KenwoodFox/EG-207/docs/advanced_service/flowcharts/flowchart.png

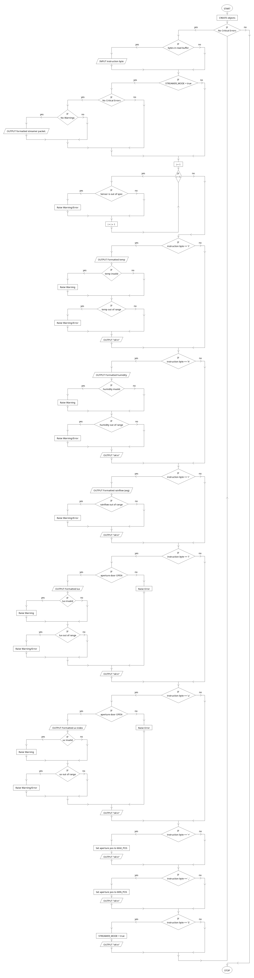
docs/advanced_service/flowcharts/flowchart.png
