KenwoodFox/EG-207/docs/presentations/resources/SNHU-CETA.png

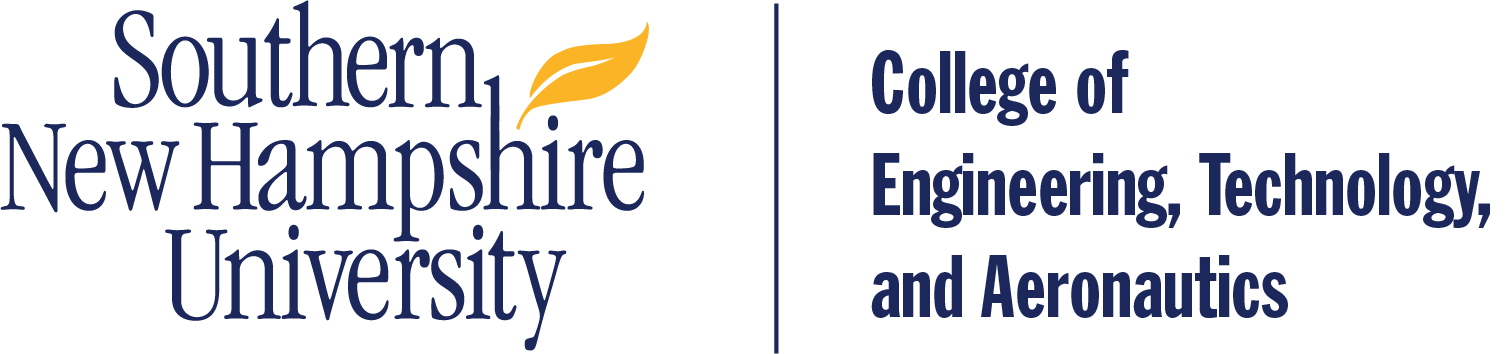
docs/presentations/resources/SNHU-CETA.png
