KenwoodFox/EG-207/docs/presentations/resources/SNHU.png

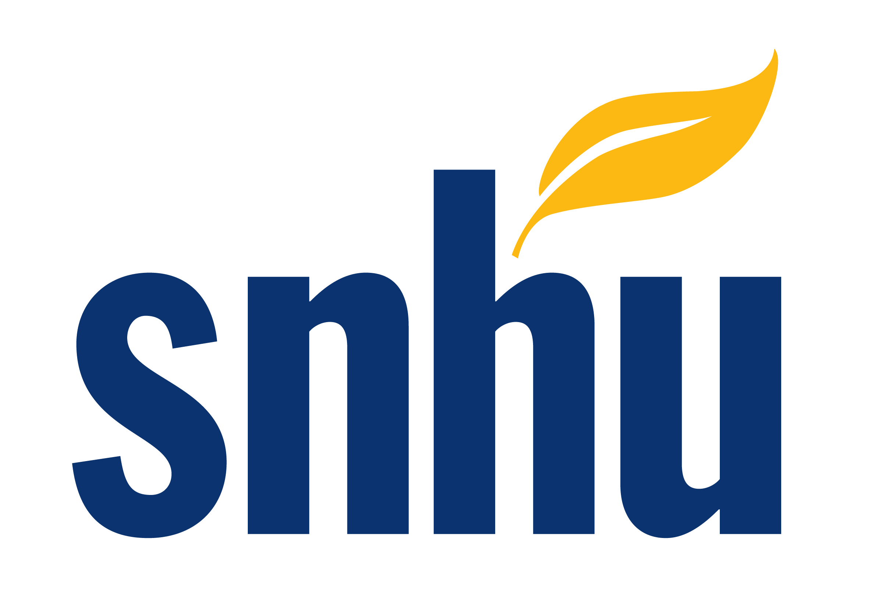
docs/presentations/resources/SNHU.png
