KenwoodFox/EG-207/CAD/schematics/lab2/lab2.sch

## KiCad design CAD/schematics/lab2/lab2.sch (2021-11-01)

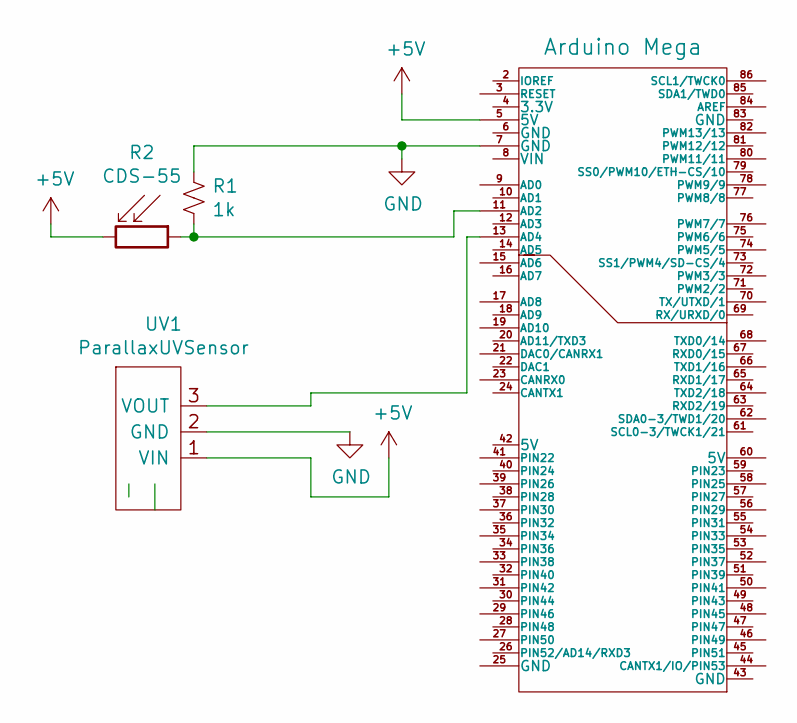
[picture p62: schematic lab2.sch]

Parts:
R1: 1k
R2: CDS-55
UV1: ParallaxUVSensor

Connections:
+5V: R2.2, UV1.1 (VIN)
GND: R1.1, UV1.2 (GND)
unnamed: R1.2, R2.1
