KenwoodFox/EG-207/python/goldstandard/goldplot.py

# Team Gold
# EG-207
# Southern New Hampshire University, 2021

import re
import csv
import time
import serial
import logging
import argparse
import subprocess

import matplotlib.pyplot as plt
import matplotlib.animation as animation
import matplotlib as mpl

from statistics import mean


class GoldPlotApp:
    def __init__(self, logger, **kwargs):
        # logging
        self.log = logger

        # Graph theme
        mpl.style.use('seaborn')

        # Parse args
        parser = argparse.ArgumentParser(description='Parse args.')
        parser.add_argument('--port',
                            nargs='?',
                            default='/dev/ttyACM0',
                            type=str)

        parser.add_argument('--data',
                            nargs='?',
                            default=None,
                            type=str)

        parser.add_argument('-o',
                            nargs='?',
                            default='output.csv',
                            type=str)

        parser.add_argument('--hist',
                            action='store_true')

        self.args = parser.parse_args()

        # Arduino version
        self.arduino_version = None

        # Software version
        self.software_version = self.get_git_revision_hash()

        # Setup graph
        self.initalize_graph()

        if self.args.data is None:
            # Log
            self.log.info("Initalizing arduino.")

            # Connect arduino
            self.arduino = serial.Serial(self.args.port, 115200, timeout=1)

            # Data for this run
            self.csv_data = open(self.args.o, 'w')
            self.csv_writer = csv.writer(self.csv_data, delimiter=',',
                                         quotechar='"',
                                         quoting=csv.QUOTE_MINIMAL)
            self.csv_writer.writerow(['Epoch Time', 'Temp', 'Humidity', 'Lux Level', 'UV Index'])  # noqa: E501

        else:
            # Load csv data instead.
            self.log.debug("Loading CSV.")
            with open(self.args.data, mode='r') as datafile:
                csv_reader = csv.DictReader(datafile)
                for row in csv_reader:
                    if isinstance(row['Epoch Time'], str):
                        _time = row["Epoch Time"]
                        _temp = row["Temp"]
                        _humid = row["Humidity"]

                        self.time_scale.append(float(_time))
                        self.temp_reading.append(float(_temp))
                        self.humidity_reading.append(float(_humid))

    def run(self):
        if self.args.data is None:
            # Setup animated graph.
            ani = animation.FuncAnimation(self.fig,
                                          self.update_graph,
                                          interval=2)

            # Just for flake
            ani.__str__()
        else:
            self.log.debug("Got to run")

            self.update_graph(0)

        # Show plot!
        plt.show()

    def get_new_frame(self):
        # Time
        now = float(time.time())
        # Frame is one data frame
        frame = self.arduino.readline().decode().strip('\n\r')

        try:
            ver_match = re.search('(?<=version )(.*)', frame).group(0)
            if ver_match is not None:
                self.arduino_version = str(ver_match)
        except AttributeError:
            pass

        try:
            if len(frame) > 0:
                # Capture a new frame
                frame = frame.split(',')
                self.log.debug(f'Raw frame is {frame}')

                self.current_humidy = float(frame[0].strip('H'))
                self.current_temp = float(frame[1].strip('T'))
                self.current_lux_level = float(frame[2].strip('L'))
                self.current_uv_index = float(frame[3].strip('U'))

                if self.current_humidy != 0 and self.current_temp != 0:
                    # Logging
                    self.log.info(f'Got new frame: {frame}')

                    # Plot scales
                    self.time_scale.append(now)
                    self.temp_reading.append(self.current_temp)
                    self.humidity_reading.append(self.current_humidy)
                    self.lux_reading.append(self.current_lux_level)
                    self.index_reading.append(self.current_uv_index)
                else:
                    logging.error(f'Error, empty frame: {frame}')
        except (IndexError, AttributeError, ValueError) as e:
            self.log.warn('Got bad frame')
            self.log.error(e)

        # Trigger a csv update
        self.write_csv()

    def write_csv(self):
        try:
            self.csv_writer.writerow([self.time_scale[-1],
                                     self.temp_reading[-1],
                                     self.humidity_reading[-1],
                                     self.lux_reading[-1],
                                     self.index_reading[-1]])
            self.log.info(f'Wrote {self.current_lux_level} to data.')
        except IndexError:
            self.log.warn("Not writing bad frame to csv.")

    def initalize_graph(self):
        # Setup figure
        self.fig = plt.figure()
        self.ax = self.fig.add_subplot(111)
        self.temp_line_plot = self.fig.add_subplot(2, 1, 1)
        self.humidity_line_plot = self.fig.add_subplot(2, 1, 2)

        # Mess
        self.time_scale = []
        self.temp_reading = []
        self.max_temp = 0
        self.max_temp_time = 0
        self.humidity_reading = []
        self.index_reading = []
        self.lux_reading = []
        self.current_humidy = float(0)
        self.current_temp = float(0)

        # Spacing
        self.fig.tight_layout(pad=3.0)

        # Turn off axis lines and ticks of the big subplot
        self.ax.spines['top'].set_color('none')
        self.ax.spines['bottom'].set_color('none')
        self.ax.spines['left'].set_color('none')
        self.ax.spines['right'].set_color('none')
        self.ax.tick_params(labelcolor='w',
                            top=False,
                            bottom=False,
                            left=False,
                            right=False)

        self.ax.set_xlabel('Time (Epoch)')

        self.temp_line_plot.set_title('Temp')
        self.humidity_line_plot.set_title('Humidity')

        self.ax.annotate(f"""Software Version {self.software_version}
                             Arduino Version {self.arduino_version}""",
                         xy=(0.3, -0.13),
                         xycoords='axes fraction',
                         horizontalalignment='right',
                         verticalalignment='top')

        self.ax.annotate('Gold Standard, Team Gold, SNHU',
                         xy=(0.2, 1.1),
                         xycoords='axes fraction',
                         horizontalalignment='right',
                         verticalalignment='top')

    def update_graph(self, i):
        try:
            if self.args.data is None:
                # Get new frame
                self.get_new_frame()

            self.temp_line_plot.clear()
            self.temp_line_plot.plot(self.time_scale,
                                     self.lux_reading,
                                     color="red")

            self.humidity_line_plot.clear()
            self.humidity_line_plot.plot(self.time_scale,
                                         self.humidity_reading,
                                         color="blue")

            # === Annotations ===
            # Max temp
            self.max_temp = max(self.temp_reading)
            self.max_temp_time = self.time_scale[
                                 self.temp_reading.index(self.max_temp)]
            self.log.debug(f"Max temp {self.max_temp}")

            # Standard deviation math
            self.temp_mean = mean(self.temp_reading)
            self.log.info(f'Mean of temp is {self.temp_mean}')

            deviations = []
            for reading in self.temp_reading:
                result = (reading - self.temp_mean) ** 2
                deviations.append(result)

            # Variance
            self.temp_variance = mean(deviations)

            self.log.debug(deviations)

            self.temp_first_deviation = self.time_scale[
                                        self.find_nearest(deviations, 1)]
            self.temp_second_deviation = self.time_scale[
                                         self.find_nearest(deviations, 2)]

            self.log.debug(f"First deviation at {self.temp_first_deviation}, second at {self.temp_second_deviation}")  # Noqa: E501

            # Annotate the max
            self.temp_line_plot.annotate('Max Temp',
                                         xy=(self.max_temp_time,
                                             self.max_temp),
                                         xycoords='data',
                                         xytext=(0.2, 0.80),
                                         textcoords='axes fraction',
                                         arrowprops=dict(facecolor='black',
                                                         shrink=0.05),
                                         horizontalalignment='right',
                                         verticalalignment='top')

            self.temp_line_plot.annotate('1st deviation',
                                         xy=(self.temp_first_deviation,
                                             self.temp_reading[self.time_scale.index(self.temp_first_deviation)]),  # Noqa: E501
                                         xycoords='data',
                                         xytext=(0.5, 0.3),
                                         textcoords='axes fraction',
                                         arrowprops=dict(facecolor='black',
                                                         shrink=0.05),
                                         horizontalalignment='right',
                                         verticalalignment='top')

            self.temp_line_plot.annotate('2nd deviation',
                                         xy=(self.temp_second_deviation,
                                             self.temp_reading[self.time_scale.index(self.temp_second_deviation)]),  # Noqa: E501
                                         xycoords='data',
                                         xytext=(0.8, 0.3),
                                         textcoords='axes fraction',
                                         arrowprops=dict(facecolor='black',
                                                         shrink=0.05),
                                         horizontalalignment='right',
                                         verticalalignment='top')

            # Calculations for sensor response
            response_value = self.find_nearest(self.temp_reading,
                                               self.max_temp * 0.993)
            reponse_time = self.time_scale[
                           self.temp_reading.index(response_value)]
            reponse_time = reponse_time - min(self.time_scale)

            self.temp_line_plot.annotate(
                            f'Sensor Response Time: {reponse_time}',
                            xy=(0.3, 1.1),
                            xycoords='axes fraction',
                            horizontalalignment='right',
                            verticalalignment='top')

            plt.show()
        except ValueError as e:
            self.log.error(e)
        except KeyboardInterrupt:
            self.log.info('Exiting safely.')
            self.close()

    def find_nearest(self, list, target):
        normalized_list = []

        for element in list:
            element = abs(target - element)
            normalized_list.append(element)

        local_min = 10
        for element in normalized_list:
            if element < local_min:
                local_min = element

        index_of_min = normalized_list.index(local_min)
        return index_of_min

    def get_git_revision_hash(self) -> str:
        return subprocess.check_output(['git', 'describe', '--abbrev=4', '--always', '--tags']).decode('ascii').strip()  # Noqa: E501

    def close(self):
        self.log.info(f'Arduino was using version {self.arduino_version}')
        self.arduino.close()
        self.csv_data.close()
        quit()
